linhlinhto/gas-concentration-sensor/Gaswarning_image/Dash_board_group1.png

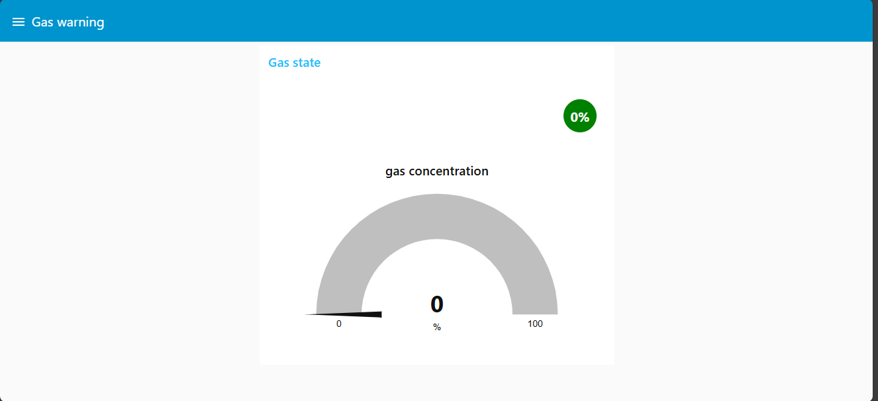
Gaswarning_image/Dash_board_group1.png
