linhlinhto/gas-concentration-sensor/Gaswarning_image/Node_Red_flow2_1.png

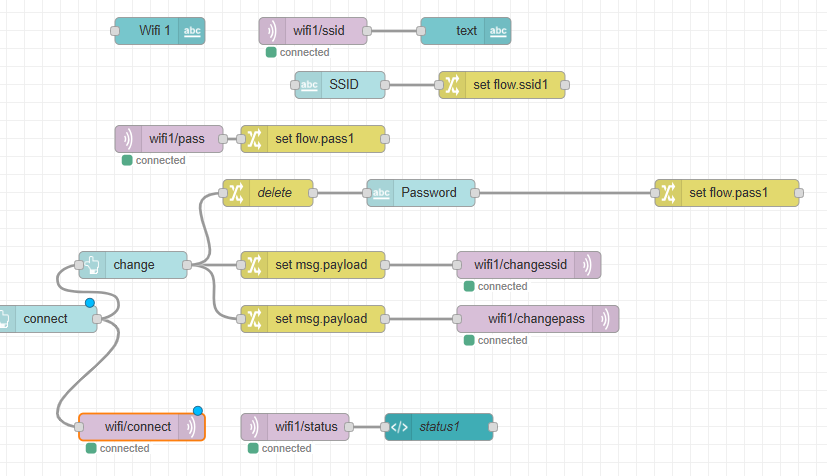
Gaswarning_image/Node_Red_flow2_1.png
