linhlinhto/gas-concentration-sensor/Gaswarning_image/Node_Red_flow2_3.png

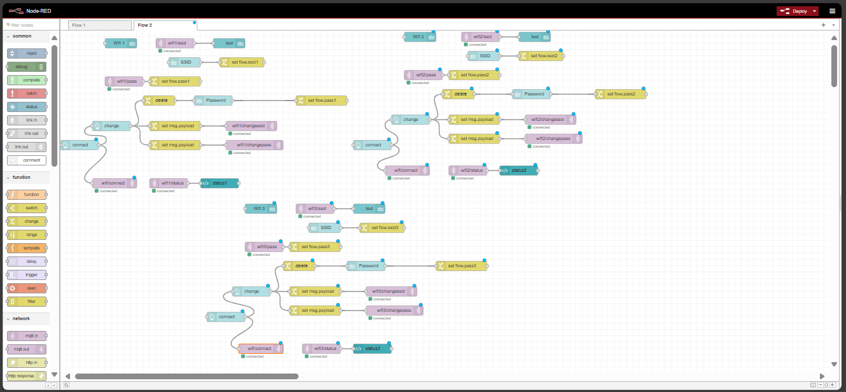
Gaswarning_image/Node_Red_flow2_3.png
