linhlinhto/gas-concentration-sensor/Gaswarning_image/web_config_wifi.png

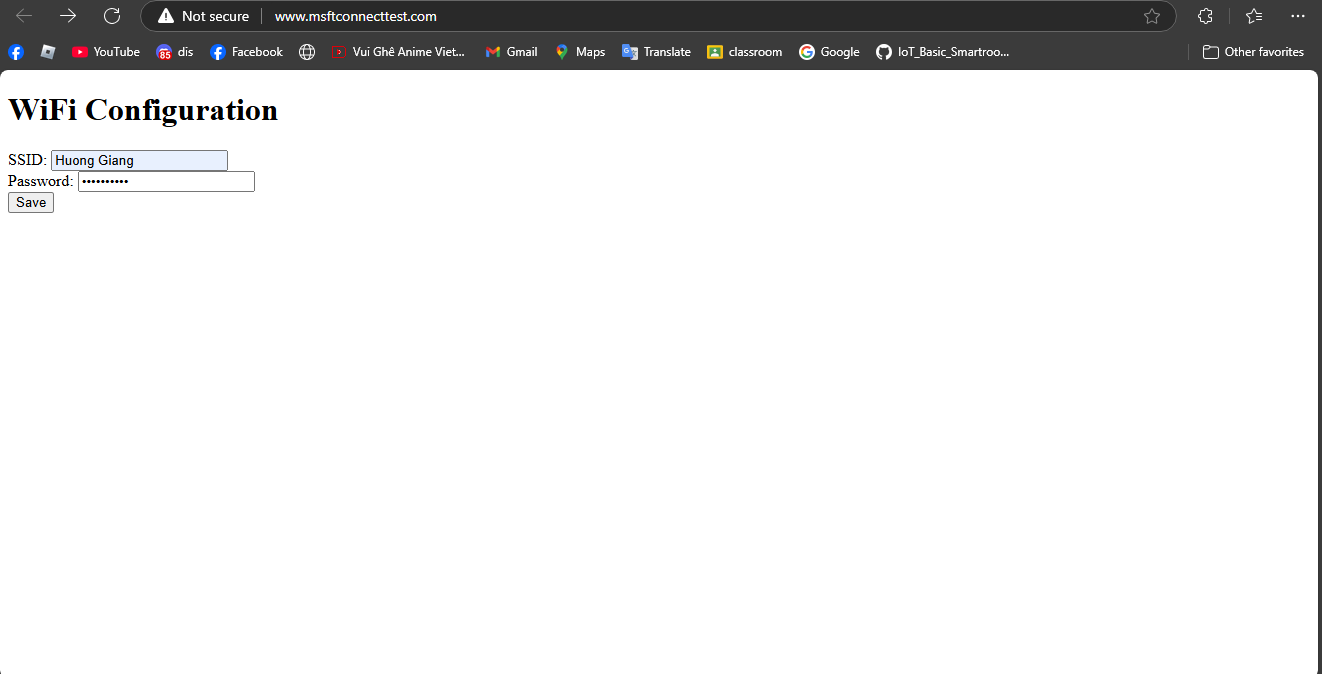
Gaswarning_image/web_config_wifi.png
