linhlinhto/gas-concentration-sensor/Gaswarning_image/Real_component2.jpg

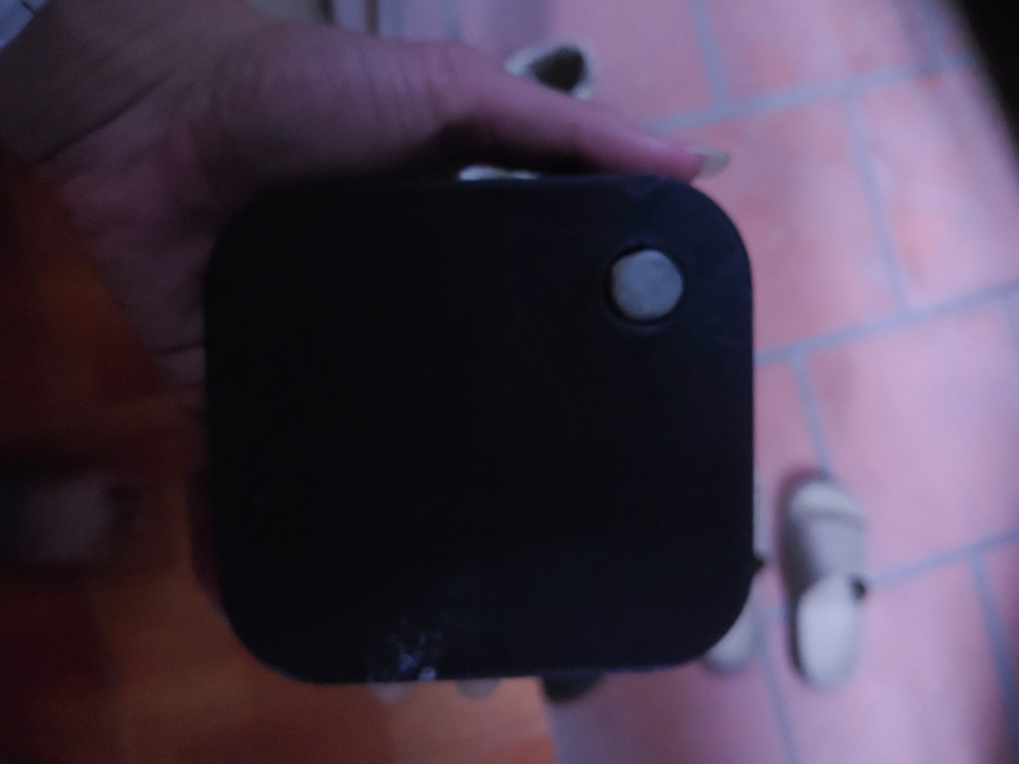
Gaswarning_image/Real_component2.jpg
